LibreDAQ/libredaq/libldaq/include/format.h

/*+-------------------------------------------------------------------------+
  |                             LibreDAQ                                    |
  |                                                                         |
  | Copyright (C) 2015  Jose Luis Blanco Claraco                            |
  | Distributed under GNU General Public License version 3                  |
  |   See <http://www.gnu.org/licenses/>                                    |
  |                                                                         |
  | NOTE: This class is derived from CSerialPort from the MRPT project:     |
  |                     Mobile Robot Programming Toolkit (MRPT)             |
  |                          http://www.mrpt.org/                           |
  |                                                                         |
  | Copyright (c) 2005-2015, Individual contributors, see AUTHORS file      |
  | See: http://www.mrpt.org/Authors - All rights reserved.                 |
  | Released under BSD License. See details in http://www.mrpt.org/License  |
  +-------------------------------------------------------------------------+  */

#pragma once

#include <string>

namespace libredaq
{
// Define a decl. modifier for printf-like format checks at compile time:
#ifdef __GNUC__
#	define MBDE_printf_format_check(_FMT_,_VARARGS_)  __attribute__ ((__format__ (__printf__, _FMT_,_VARARGS_)))
#else
#	define MBDE_printf_format_check(_FMT_,_VARARGS_)
#endif
	
	/** A sprintf-like function for std::string */
	std::string format(const char *fmt, ...) MBDE_printf_format_check(1,2);

} // End of namespace
